WilliTourt/ESP32-Keyboard-Customized/ESP32-C3 BLE Keybrick/src/char.c

#include "char.h"

const uint8_t OLED_ASCII6x8[][6] = {

	0x00,0x00,0x00,0x00,0x00,0x00,//   0
	0x00,0x00,0x00,0x2F,0x00,0x00,// ! 1
	0x00,0x00,0x07,0x00,0x07,0x00,// " 2
	0x00,0x14,0x7F,0x14,0x7F,0x14,// # 3
	0x00,0x24,0x2A,0x7F,0x2A,0x12,// $ 4
	0x00,0x23,0x13,0x08,0x64,0x62,// % 5
	0x00,0x36,0x49,0x55,0x22,0x50,// & 6
	0x00,0x00,0x00,0x07,0x00,0x00,// ' 7
	0x00,0x00,0x1C,0x22,0x41,0x00,// ( 8
	0x00,0x00,0x41,0x22,0x1C,0x00,// ) 9
	0x00,0x14,0x08,0x3E,0x08,0x14,// * 10
	0x00,0x08,0x08,0x3E,0x08,0x08,// + 11
	0x00,0x00,0x00,0xA0,0x60,0x00,// , 12
	0x00,0x08,0x08,0x08,0x08,0x08,// - 13
	0x00,0x00,0x60,0x60,0x00,0x00,// . 14
	0x00,0x20,0x10,0x08,0x04,0x02,// / 15
	0x00,0x3E,0x51,0x49,0x45,0x3E,// 0 16
	0x00,0x00,0x42,0x7F,0x40,0x00,// 1 17
	0x00,0x42,0x61,0x51,0x49,0x46,// 2 18
	0x00,0x21,0x41,0x45,0x4B,0x31,// 3 19
	0x00,0x18,0x14,0x12,0x7F,0x10,// 4 20
	0x00,0x27,0x45,0x45,0x45,0x39,// 5 21
	0x00,0x3C,0x4A,0x49,0x49,0x30,// 6 22
	0x00,0x01,0x71,0x09,0x05,0x03,// 7 23
	0x00,0x36,0x49,0x49,0x49,0x36,// 8 24
	0x00,0x06,0x49,0x49,0x29,0x1E,// 9 25
	0x00,0x00,0x36,0x36,0x00,0x00,// : 26
	0x00,0x00,0x56,0x36,0x00,0x00,// ; 27
	0x00,0x08,0x14,0x22,0x41,0x00,// < 28
	0x00,0x14,0x14,0x14,0x14,0x14,// = 29
	0x00,0x00,0x41,0x22,0x14,0x08,// > 30
	0x00,0x02,0x01,0x51,0x09,0x06,// ? 31
	0x00,0x3E,0x49,0x55,0x59,0x2E,// @ 32
	0x00,0x7C,0x12,0x11,0x12,0x7C,// A 33
	0x00,0x7F,0x49,0x49,0x49,0x36,// B 34
	0x00,0x3E,0x41,0x41,0x41,0x22,// C 35
	0x00,0x7F,0x41,0x41,0x22,0x1C,// D 36
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
// 	0x00,0x00,0x00,0x00,0x00,0x00,0x00,0x03,0x3F,0x3F,0x3F,0x3F,0x1F,0x1F,0x1F,0x1F,
// 	0x0F,0x1F,0x0F,0x0F,0x07,0x01,0x00,0x00,0x00,0x00,0x00,0x00,0x00,0x00,0x00,0x00,
// 	0xC0,0xF0,0xF8,0xFE,0xFF,0xFF,0xFF,0xFF,0xFF,0xFF,0xFF,0xFF,0xFF,0xFF,0xFF,0xFF

// };
