WilliTourt/ESP32-Keyboard-Customized/ESP32-C3 BLE Keybrick/src/iic.c

#include "iic.h"

static IIC_BusCfg IIC_Bus[8];

/**
	* @brief  软件IIC初始化函数
	* @param  SCL SCL引脚号
	* @param  SDA SDA引脚号
	* @param  spd IIC速度，此值为每次读写后的延时，单位为us
	* @param  bus 当前操作的软件IIC总线号，范围 0-7
	* @retval None
	*/
void IIC_Init(uint8_t SCL, uint8_t SDA, uint8_t spd, uint8_t bus) {

	IIC_Bus[bus].SCL_Pin = SCL;
	IIC_Bus[bus].SDA_Pin = SDA;
	IIC_Bus[bus].Delay = spd;

    pinMode(OLED_SCL, OUTPUT);
    pinMode(OLED_SDA, OUTPUT);

	digitalWrite(SCL, HIGH);
	digitalWrite(SDA, HIGH);
}

void wSCL(uint8_t bus, uint8_t state) {
	digitalWrite(IIC_Bus[bus].SCL_Pin, state);
	if (IIC_Bus[bus].Delay > 0) {
		delayMicroseconds(IIC_Bus[bus].Delay);
	}
}

void wSDA(uint8_t bus, uint8_t state) {
	digitalWrite(IIC_Bus[bus].SDA_Pin, state);
	if (IIC_Bus[bus].Delay > 0) {
		delayMicroseconds(IIC_Bus[bus].Delay);
	}
}

uint8_t rSDA(uint8_t bus) {
	uint8_t state = digitalRead(IIC_Bus[bus].SDA_Pin);
	if (IIC_Bus[bus].Delay > 0) {
		delayMicroseconds(IIC_Bus[bus].Delay);
	}
	return state;
}

/**
	* @brief  软件IIC开始信号
	* @param  bus 当前操作的软件IIC总线号，范围 0-7
	* @retval None
	*/
void IIC_Start(uint8_t bus) {
	wSDA(bus, HIGH);
	wSCL(bus, HIGH);

	wSDA(bus, LOW);
	wSCL(bus, LOW);
}

/**
	* @brief  软件IIC结束信号
	* @param  bus 当前操作的软件IIC总线号，范围 0-7
	* @retval None
	*/
void IIC_Stop(uint8_t bus) {
	wSDA(bus, LOW);
	wSCL(bus, HIGH);

	wSDA(bus, HIGH);
}

/**
	* @brief  软件IIC发送一个字节
	* @param  bus 当前操作的软件IIC总线号，范围 0-7
	* @param  Byte 需要发送的字节
	* @retval None
	*/
void IIC_SendByte(uint8_t bus, uint8_t byte) {
	uint8_t i;
	for (i = 0; i < 8; i++) {
		wSDA(bus, byte & (0x80 >> i));
		wSCL(bus, HIGH);
		wSCL(bus, LOW);
	}

	//// // 额外的一个时钟，不处理应答信号
	//// wSCL(bus, HIGH);
	//// wSCL(bus, LOW);
}

/**
	* @brief  软件IIC读取一个字节
	* @param  bus 当前操作的软件IIC总线号，范围 0-7
	* @retval byte 获取到的字节
	*/
uint8_t IIC_ReadByte(uint8_t bus) {
	uint8_t byte = 0x00;
	uint8_t i;
	wSCL(bus, LOW); ////
	wSDA(bus, HIGH);

	for (i = 0; i < 8; i++) {
		wSCL(bus, HIGH);
		if (rSDA(bus) == HIGH) {
			byte |= (0x80 >> i);
		}
		wSCL(bus, LOW);
	}

	return byte;
}

/**
	* @brief  软件IIC接收应答
	* @param  bus 当前操作的软件IIC总线号，范围 0-7
	* @retval ack, 0应答, 1不应答
	*/
uint8_t IIC_RcvACK(uint8_t bus) {
	uint8_t ack;
	wSCL(bus, LOW); ////
	wSDA(bus, HIGH);

	wSCL(bus, HIGH);
	ack = rSDA(bus);
	wSCL(bus, LOW);

	return ack;
}

/**
	* @brief  软件IIC发送应答
	* @param  bus 当前操作的软件IIC总线号，范围 0-7
	* @param  ack 应答信息, 0应答, 1不应答
	* @retval None
	*/
void IIC_SendACK(uint8_t bus, uint8_t ack) {
	wSCL(bus, LOW); ////
	wSDA(bus, ack);
	wSCL(bus, HIGH);
	wSCL(bus, LOW);
}
