WilliTourt/ESP32-Keyboard-Customized/ESP32-C3 BLE Keybrick/src/battery.c

#include "battery.h"

bool BAT_IS_LOW = false;

float BAT_Voltage = 0.0;

/**
  * @brief  Read battery Volt. and check if it is low.
  * @note   Data storaged in: float BAT_Voltage
  * @param  None
  * @retval None
  */
void BAT_Read() {
    static uint32_t batReadStartTime = 0;

    if (batReadStartTime == 0) {
        batReadStartTime = millis();
    } else if (millis() - batReadStartTime > BAT_READ_TIME_GAP) {

        uint16_t adcValue = analogRead(ADC_PIN);
        float adcVoltage = (float)adcValue * ADC_VREF / 4096.0;
        BAT_Voltage = adcVoltage / BAT_VOLT_DIVIDER;
        (BAT_Voltage < BAT_LOW) ? (BAT_IS_LOW = true) : (BAT_IS_LOW = false);

        batReadStartTime = 0;
    }

    // return BAT_Voltage;
}

/**
  * @brief  Get battery percentage.
  * @param  None
  * @retval uint8_t BAT_Percentage
  */
uint8_t BAT_GetPercentage() {
    uint8_t batPercentage = (BAT_Voltage - BAT_EMPTY) / (BAT_FULL - BAT_EMPTY) * 100;
    batPercentage = (batPercentage > 100) ? 100 : batPercentage;
    return batPercentage;
}
